IoanaBoari/e-book-reader/Images/Battery1.png

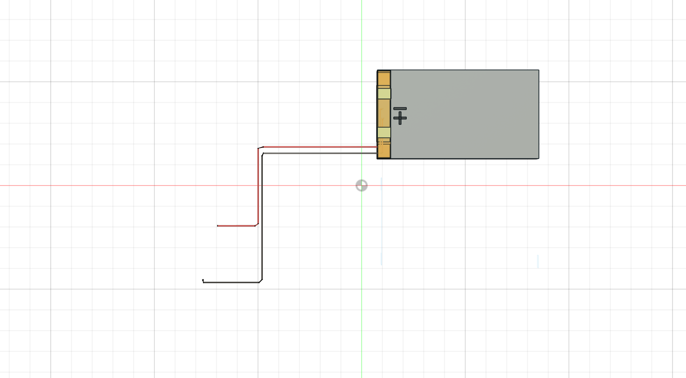
Images/Battery1.png
