IoanaBoari/e-book-reader/Images/Battery2.png

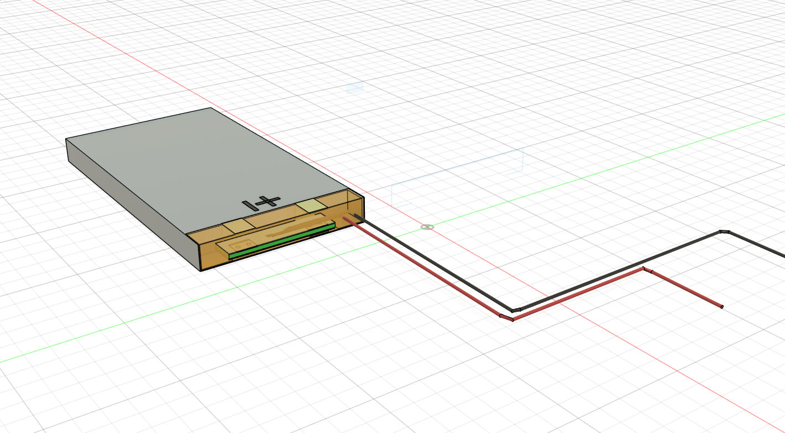
Images/Battery2.png
