IoanaBoari/e-book-reader/Images/Board2.png

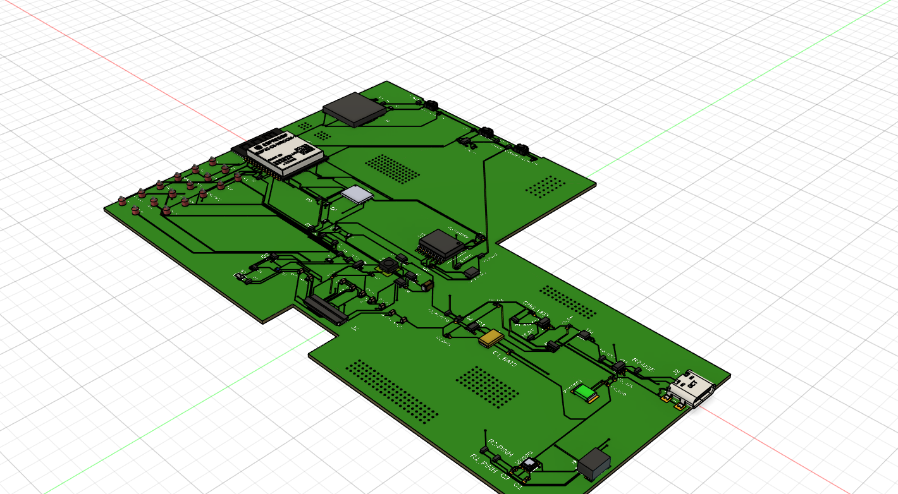
Images/Board2.png
