IoanaBoari/e-book-reader/Images/Board3.png

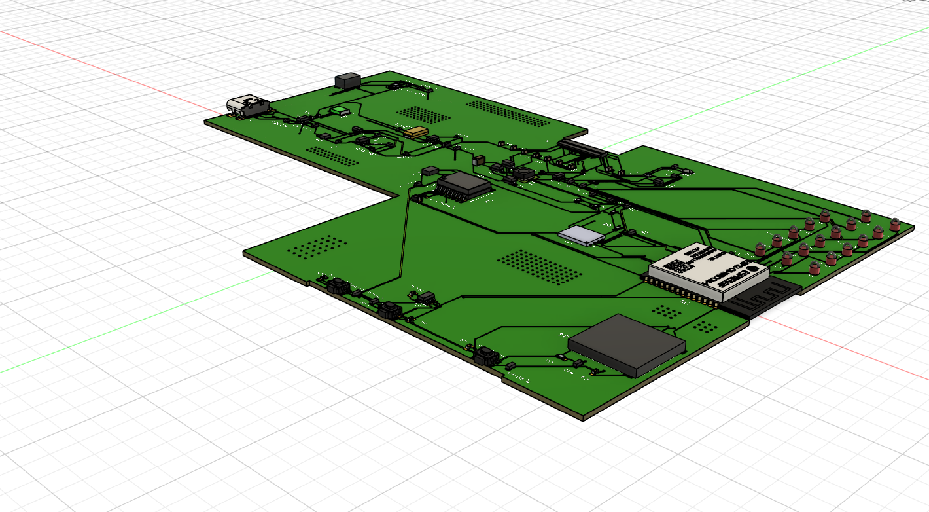
Images/Board3.png
