IoanaBoari/e-book-reader/Images/Dispozitiv2.png

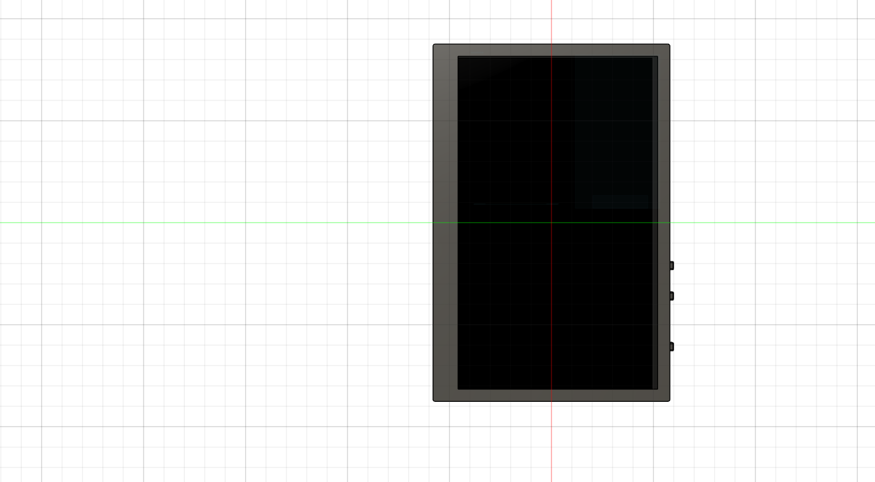
Images/Dispozitiv2.png
