IoanaBoari/e-book-reader/Images/Dispozitiv4.png

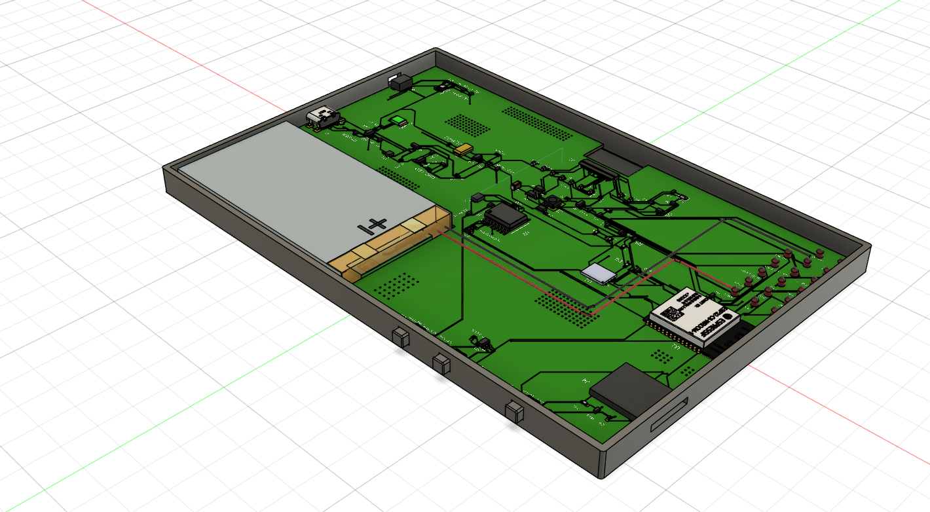
Images/Dispozitiv4.png
