IoanaBoari/e-book-reader/Images/Dispozitiv5.png

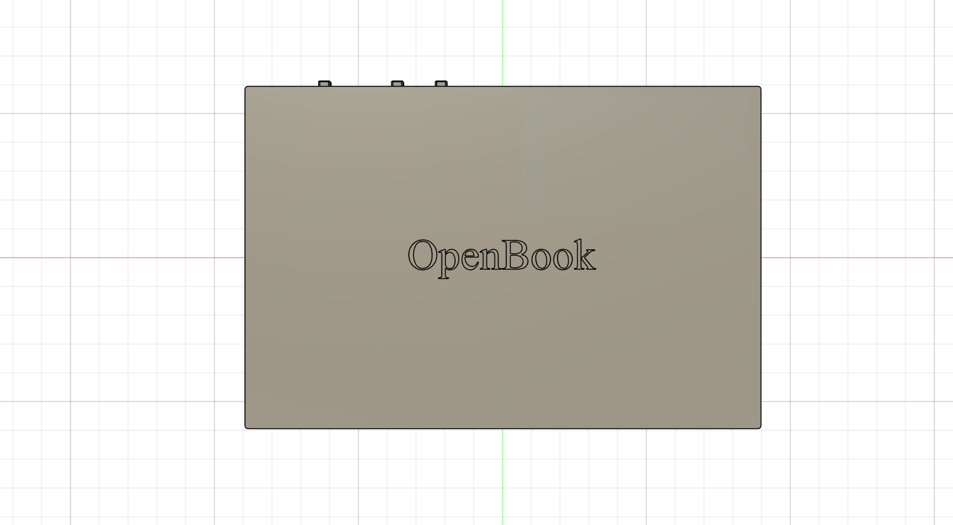
Images/Dispozitiv5.png
